DaisyAge12/FDSStick/images/2.jpg

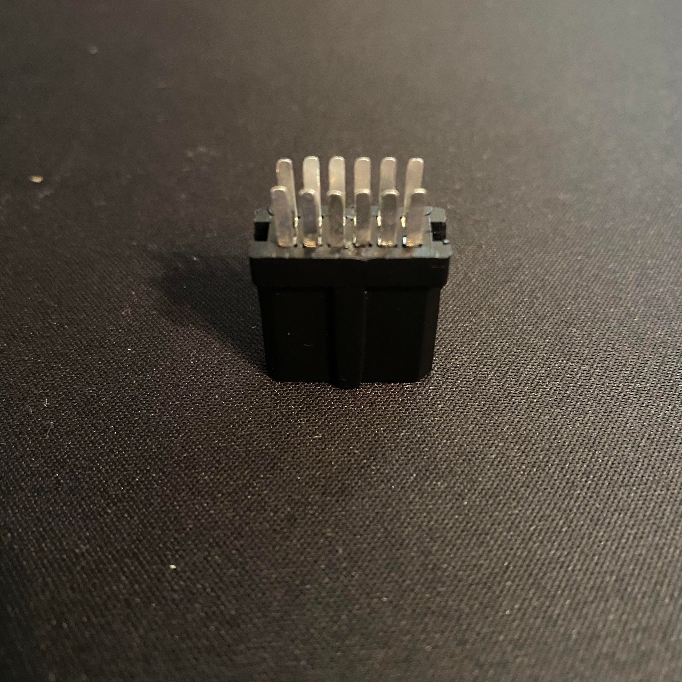
images/2.jpg
