DaisyAge12/FDSStick/images/3.jpg

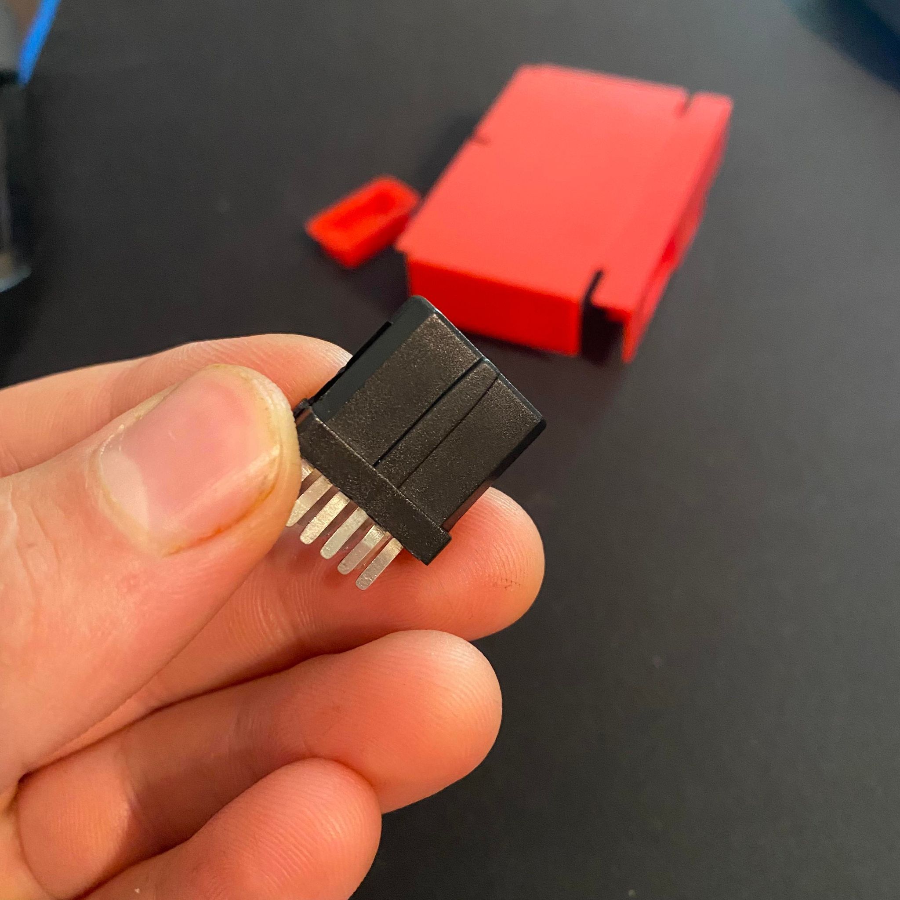
images/3.jpg
